LRIMa-Qc/iot_obj-sicro-sensor/code/broadcaster/src/drivers/sht4x.h

/**
 * sht4x.h
 *
 * SHT4X driver wrapper using Zephyr sensor API.
 *
 * Author: Nils Lahaye (2026)
 */

#ifndef SHT4X_H_
#define SHT4X_H_

#include "../utils.h"
#include <zephyr/device.h>
#include <zephyr/drivers/sensor.h>
#include <zephyr/kernel.h>
#include <zephyr/logging/log.h>


int sht4x_init(void);

int sht4x_read(float *temperature, float *humidity);

#endif /* SHT4X_H_ */
